atinfinity/m5stamp_uwb_rtls/firmware/anchor/src/main.cpp

// アンカー FW (応答専用, DS-TWR / SS-TWR 両対応)
// 自局アドレス(NODE_ADDR)宛の測距要求に応答し続ける。
// 方式は build env で切替: env:anchor = DS (既定) / env:anchor_ss = SS (-DUSE_SS_TWR)。
// タグ側と方式を揃えること。rtls-design.md §4.3 / ds-twr-design.md §3 / ss-twr-design.md §3 参照。
#include <Arduino.h>
#include <M5Stamp_UWB.h>
#include <rtls_common.h>

#ifndef NODE_ADDR
#define NODE_ADDR 0x0010
#endif

static M5Stamp_UWB uwb;

static uint32_t okCount      = 0;
static uint32_t ignoredCount = 0;  // 他アンカー宛の Poll (多アンカー環境では正常)
static uint32_t errCount     = 0;
static uint32_t lastReport = 0;

static void initUwbOrHalt() {
    while (!uwb.begin(rtls::makeUwbConfig(), rtls::makePhyConfig())) {
        Serial.printf("# uwb begin failed: %s — retrying\n", uwb.lastErrorName());
        uwb.hardReset();
        delay(1000);
    }
#ifdef USE_SS_TWR
    const char* mode = "SS";
#else
    const char* mode = "DS";
#endif
    Serial.printf("# anchor addr=0x%04X mode=%s chip=%s id=0x%08lX\n", (unsigned)NODE_ADDR,
                  mode, uwb.chipName(), (unsigned long)uwb.deviceId());
}

void setup() {
    Serial.begin(115200);
    delay(1000);
    initUwbOrHalt();
}

void loop() {
    // initiatorAddress はワイルドカード的に扱えないため、応答側は自局を
    // responder に設定して待ち受ける。相手 (initiator) は結果から知る。
#ifdef USE_SS_TWR
    M5Stamp_UWBResponderResult res =
        uwb.respondRange(rtls::makeSsRangeConfig(rtls::kTagAddrBase, NODE_ADDR));
#else
    M5Stamp_UWBDSResponderResult res =
        uwb.respondDSRange(rtls::makeDsRangeConfig(rtls::kTagAddrBase, NODE_ADDR));
#endif
    if (res.success) {
        okCount++;
    } else if (res.error == M5Stamp_UWBError::RangeFrameMismatch) {
        // 他アンカー宛の Poll を受信した (dst 不一致)。同一セルの他アンカーの交換を
        // 毎サイクル聞くので、エラーではなく ignored として数える (Issue #43)。
        ignoredCount++;
    } else if (res.error != M5Stamp_UWBError::RxTimeout) {
        // 待機中のタイムアウトは正常。それ以外のみ数える。
        errCount++;
    }

    // 10 秒ごとに統計を出力(シリアル負荷を抑える)
    uint32_t now = millis();
    if (now - lastReport >= 10000) {
        Serial.printf("# ok=%lu ignored=%lu err=%lu heap=%lu\n", (unsigned long)okCount,
                      (unsigned long)ignoredCount, (unsigned long)errCount,
                      (unsigned long)ESP.getFreeHeap());
        lastReport = now;
    }
}
